LDZPLN1/SAMD51-GPS/SAMD51 GPS.kicad_sch

## KiCad design SAMD51 GPS.kicad_sch (2022-03-28)

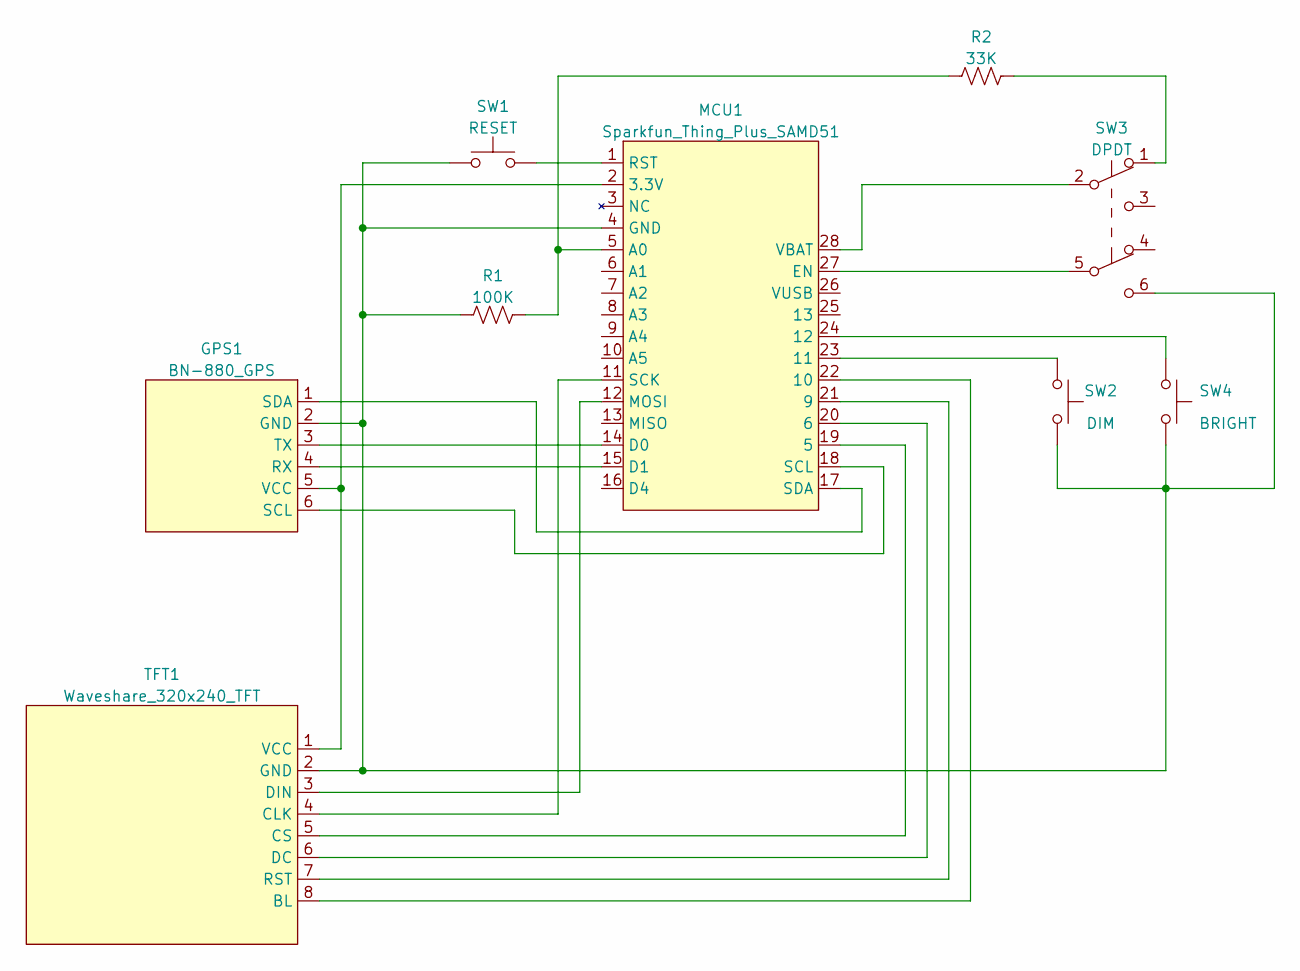
[picture p2: schematic SAMD51 GPS.kicad_sch]

Parts:
GPS1: BN-880_GPS
MCU1: Sparkfun_Thing_Plus_SAMD51
R1: 100K
R2: 33K
SW1: RESET
SW2: DIM
SW3: DPDT
SW4: BRIGHT
TFT1: Waveshare_320x240_TFT

Connections:
unnamed: GPS1.1 (SDA), MCU1.17 (SDA)
unnamed: GPS1.2 (GND), MCU1.4 (GND), R1.1, SW1.1, SW2.2, SW3.6 (C), SW4.2, TFT1.2 (GND)
unnamed: GPS1.3 (TX), MCU1.14 (D0)
unnamed: GPS1.4 (RX), MCU1.15 (D1)
unnamed: GPS1.5 (VCC), MCU1.2 (3.3V), TFT1.1 (VCC)
unnamed: GPS1.6 (SCL), MCU1.18 (SCL)
unnamed: MCU1.1 (RST), SW1.2
unnamed: MCU1.5 (A0), R1.2, R2.1
unnamed: MCU1.11 (SCK), TFT1.4 (CLK)
unnamed: MCU1.12 (MOSI), TFT1.3 (DIN)
unnamed: MCU1.19 (5), TFT1.5 (CS)
unnamed: MCU1.20 (6), TFT1.6 (DC)
unnamed: MCU1.21 (9), TFT1.7 (RST)
unnamed: MCU1.22 (10), TFT1.8 (BL)
unnamed: MCU1.23 (11), SW2.1
unnamed: MCU1.24 (12), SW4.1
unnamed: MCU1.27 (EN), SW3.5 (B)
unnamed: MCU1.28 (VBAT), SW3.2 (B)
unnamed: R2.2, SW3.1 (A)
